hzeller/digi-spherometer/img/prototype-board.jpg

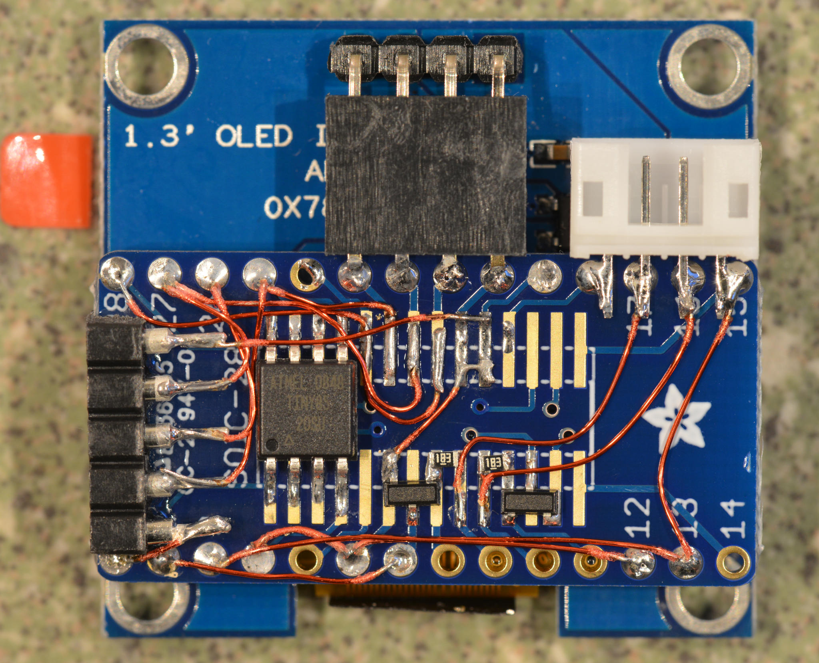
img/prototype-board.jpg
