hzeller/digi-spherometer/img/spherometer-prototype.jpg

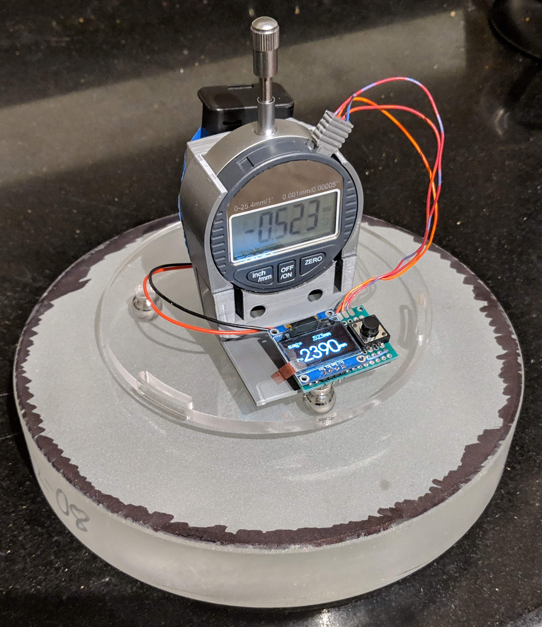
img/spherometer-prototype.jpg
